uwnrg/chip/electrical/documentation/circuit/AttachScreen.jpg

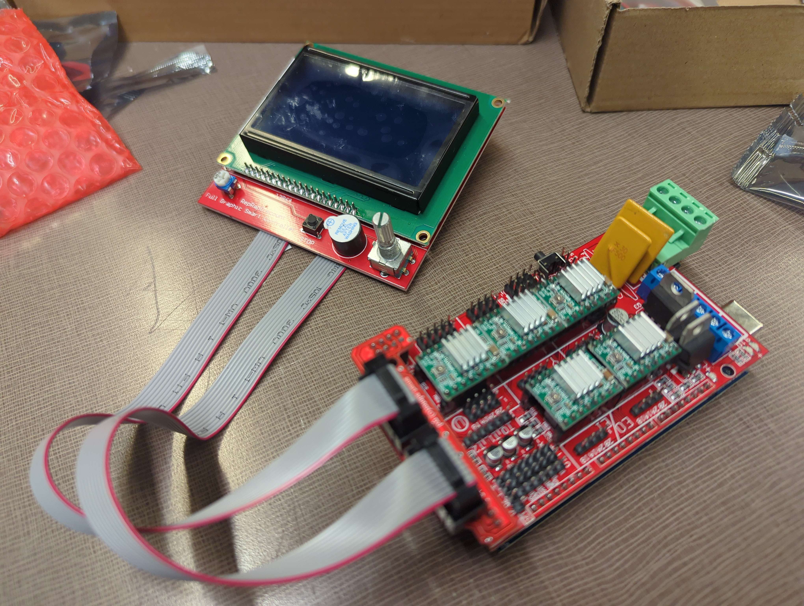
electrical/documentation/circuit/AttachScreen.jpg
