uwnrg/chip/electrical/documentation/fluid/FluidIntegration.png

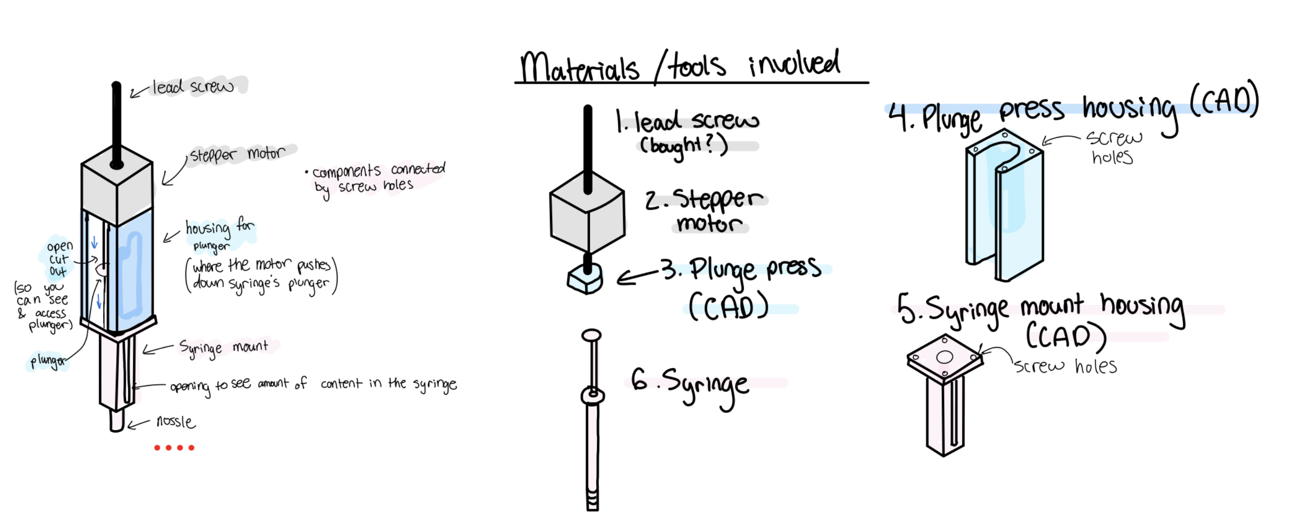
electrical/documentation/fluid/FluidIntegration.png
