uwnrg/chip/electrical/documentation/psu/PSUCase.jpg

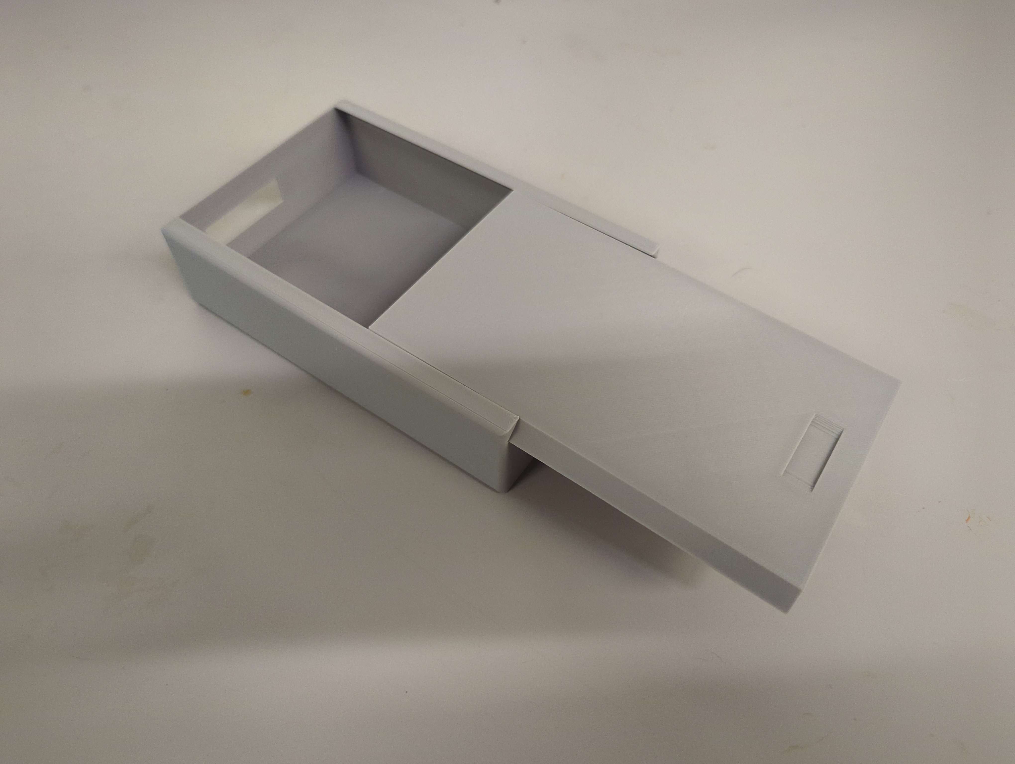
electrical/documentation/psu/PSUCase.jpg
