uwnrg/chip/electrical/documentation/psu/PSUTesting.jpg

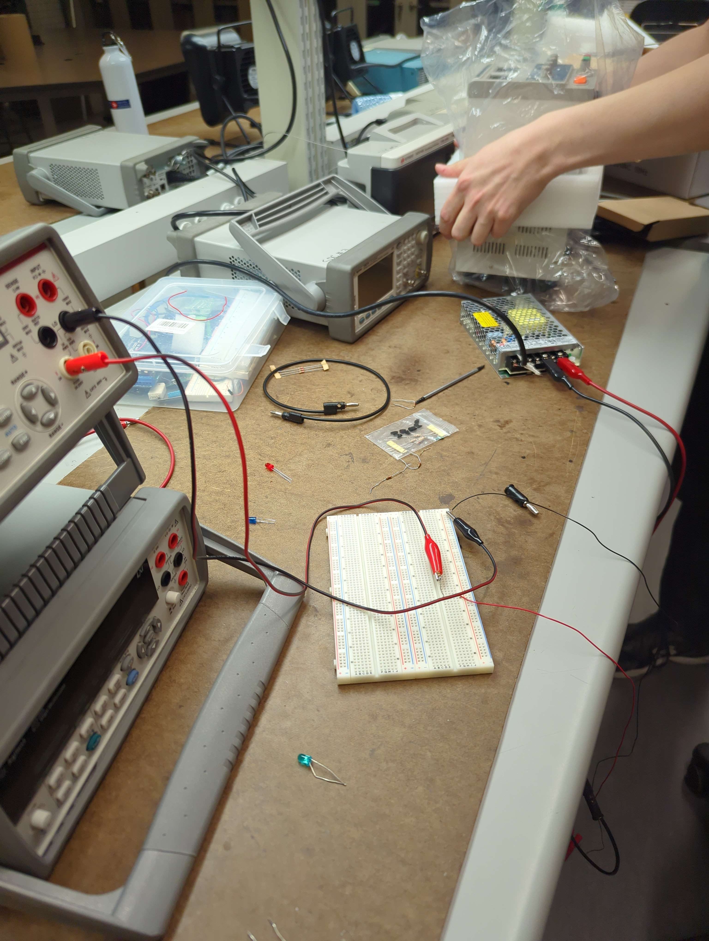
electrical/documentation/psu/PSUTesting.jpg
