uwnrg/chip/mechanical/part/LBracket.SLDPRT

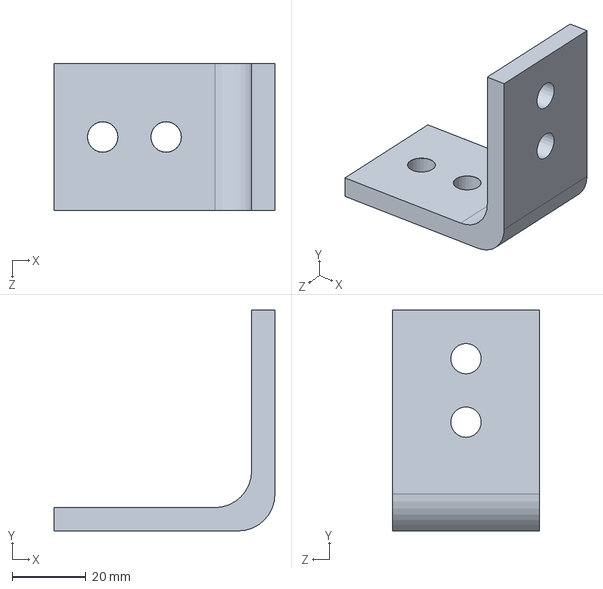
[picture p23: CAD file, 2025-01-30]
mechanical/part/LBracket.SLDPRT
60.0 x 60.0 x 40.0 mm
