uwnrg/chip/mechanical/part/LinearRod.SLDPRT

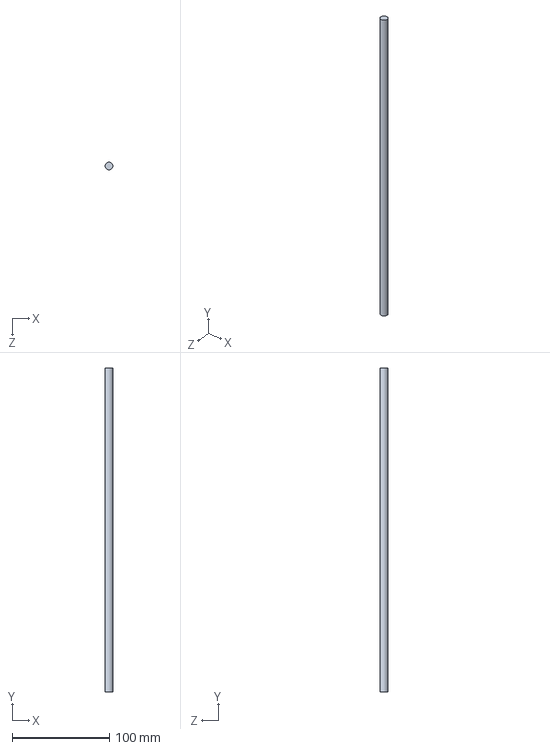
[picture p24: CAD file, 2025-01-30]
mechanical/part/LinearRod.SLDPRT
7.98 x 332.5 x 8.00 mm
