uwnrg/chip/mechanical/part/ThreadedRodNut.step

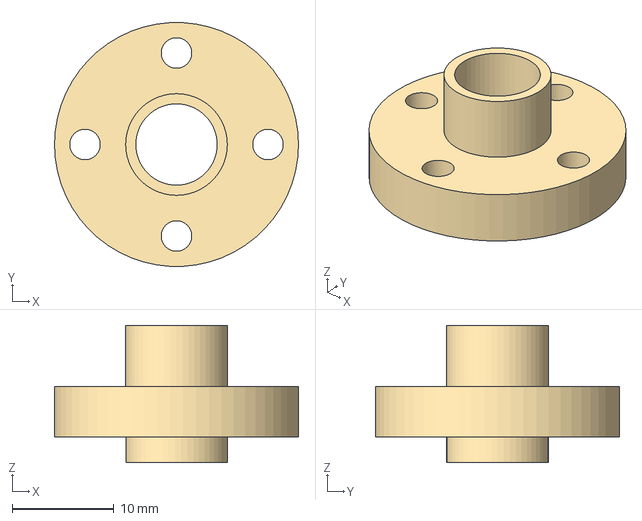
[picture p25: CAD file, 2025-01-30]
mechanical/part/ThreadedRodNut.step
24.0 x 24.0 x 13.5 mm
