uwnrg/chip/mechanical/part/ZTopBracket.SLDPRT

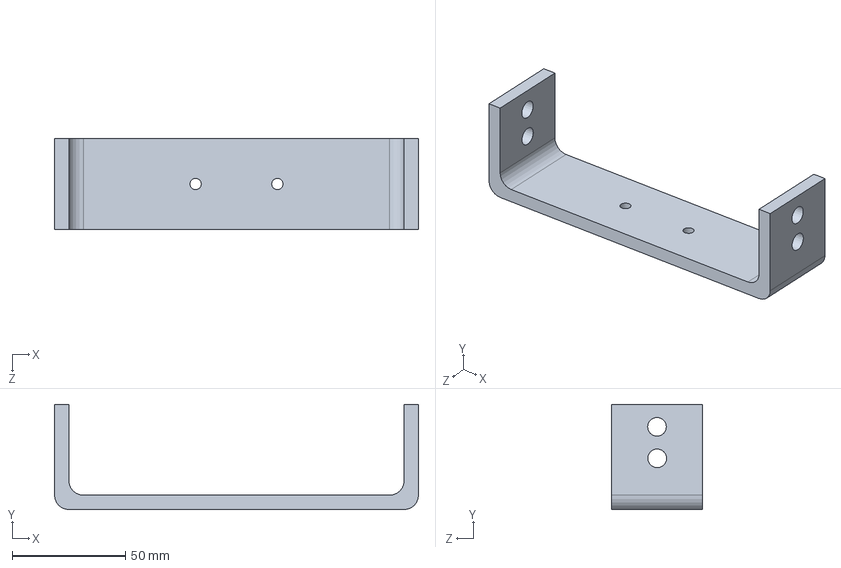
[picture p26: CAD file, 2025-01-30]
mechanical/part/ZTopBracket.SLDPRT
160.4 x 46.3 x 40.0 mm
