uwnrg/chip/electrical/documentation/circuit/ComponentsAssembly.png

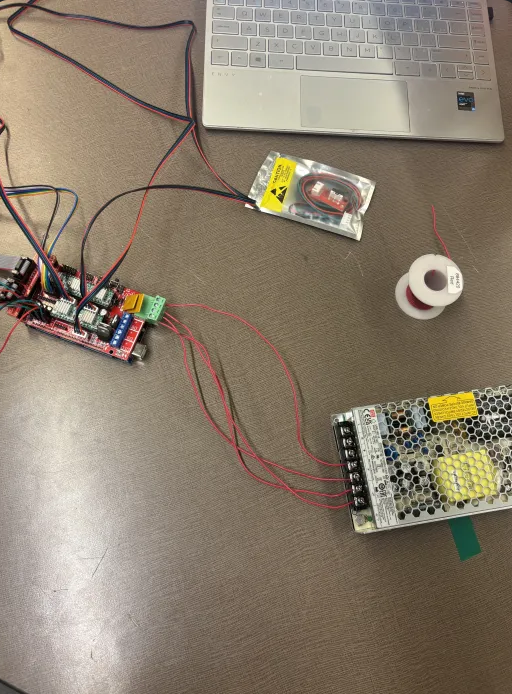
electrical/documentation/circuit/ComponentsAssembly.png
