uwnrg/chip/electrical/documentation/circuit/PSBAssembly.png

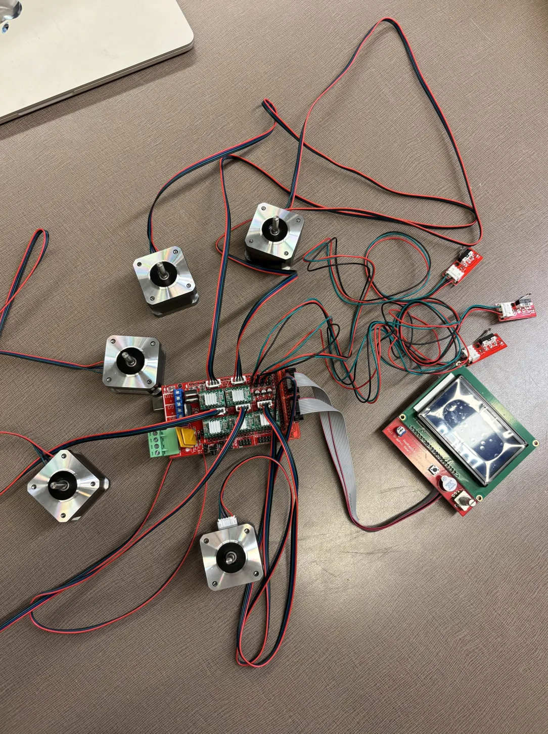
electrical/documentation/circuit/PSBAssembly.png
