uwnrg/chip/electrical/documentation/circuit/ScuffWiring.jpg

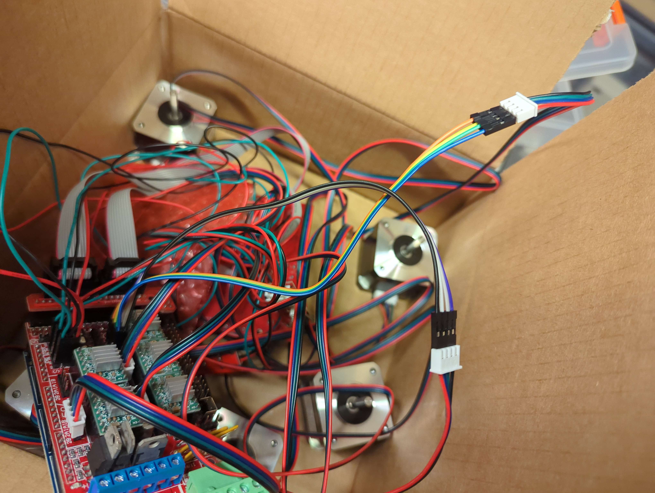
electrical/documentation/circuit/ScuffWiring.jpg
