uwnrg/chip/electrical/documentation/voltera/TestPrint.jpg

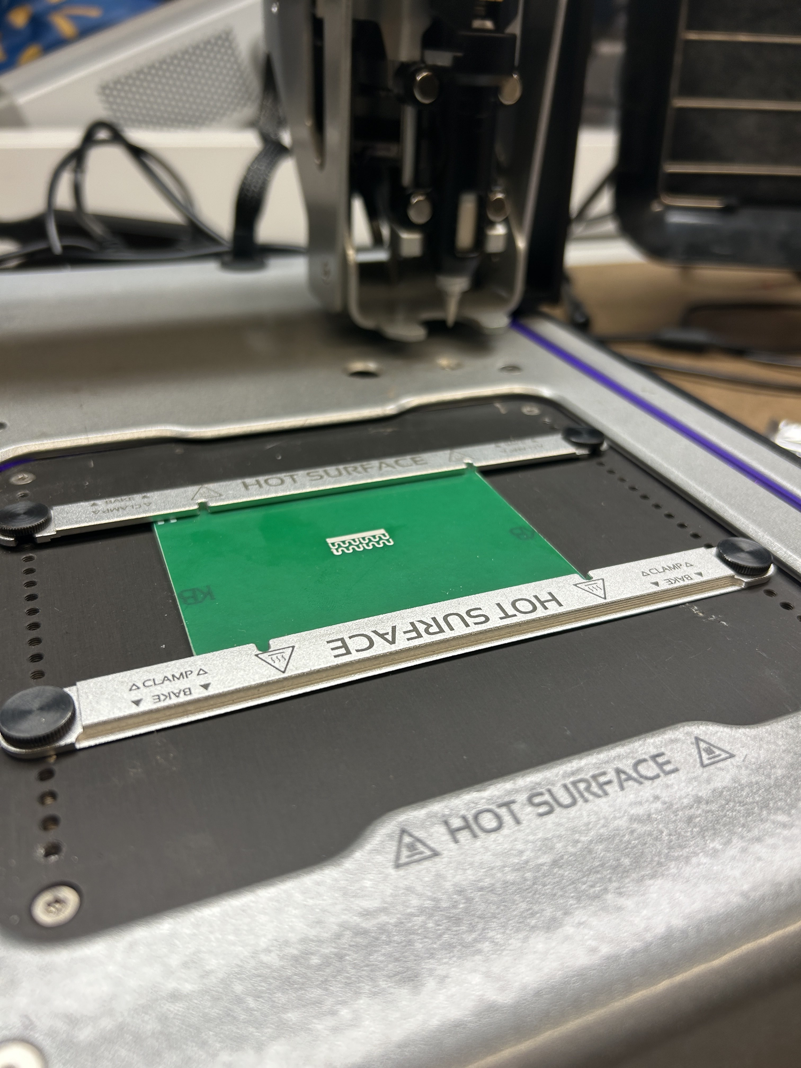
electrical/documentation/voltera/TestPrint.jpg
