uwnrg/chip/electrical/documentation/psu/testschematic.png

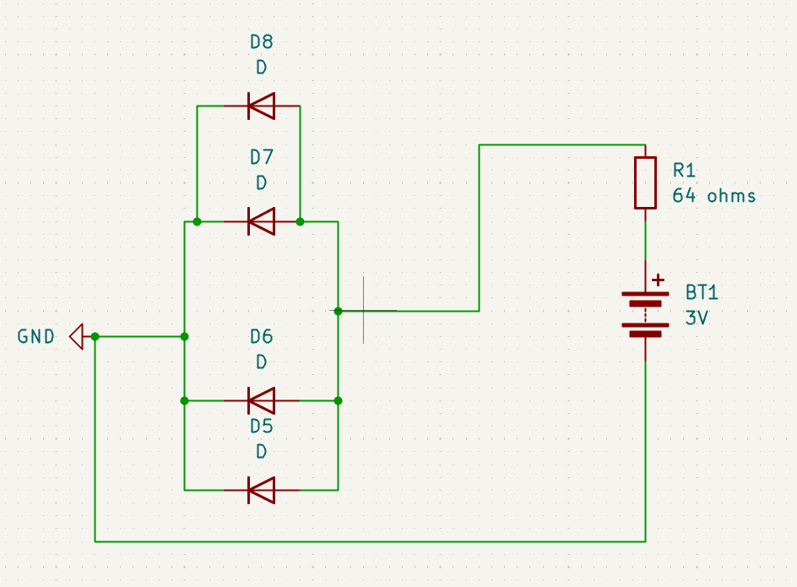
electrical/documentation/psu/testschematic.png
