uwnrg/chip/electrical/documentation/voltera/SolderingTest.jpg

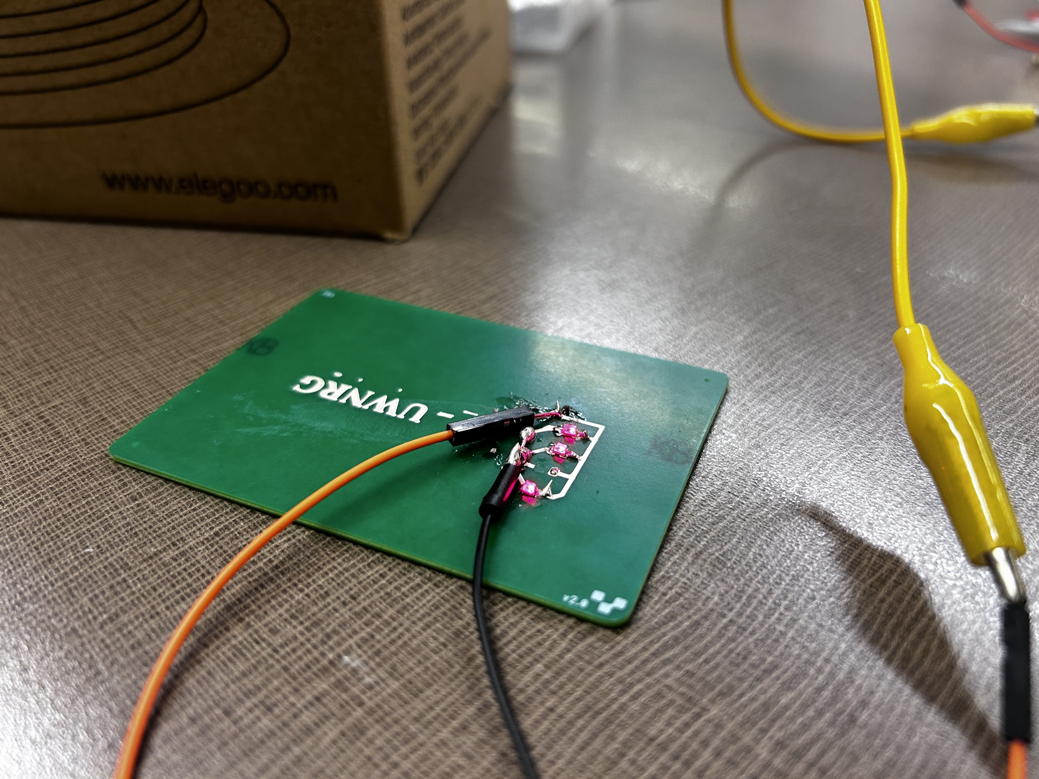
electrical/documentation/voltera/SolderingTest.jpg
