uwnrg/chip/electrical/documentation/voltera/VolteraTestLayout.png

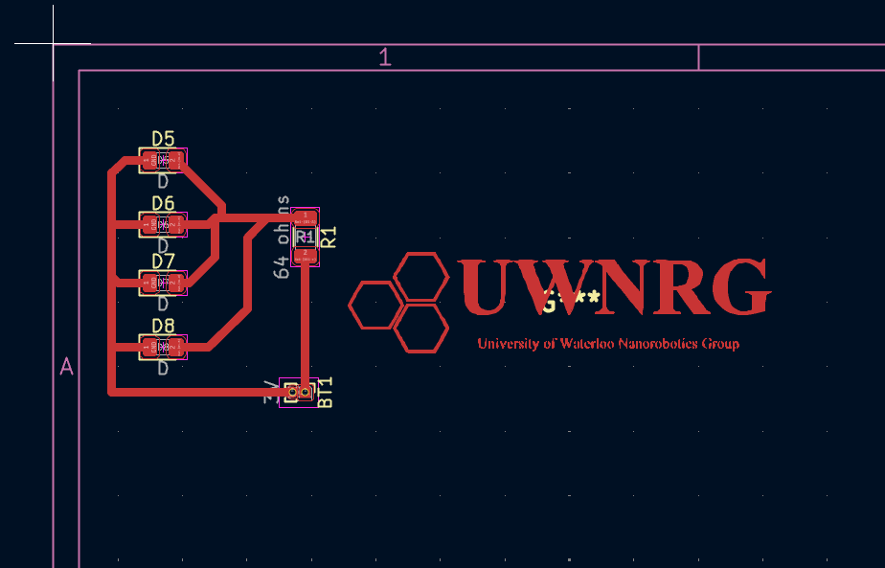
electrical/documentation/voltera/VolteraTestLayout.png
